alrevuelta/tubescreamer/img/img1.png

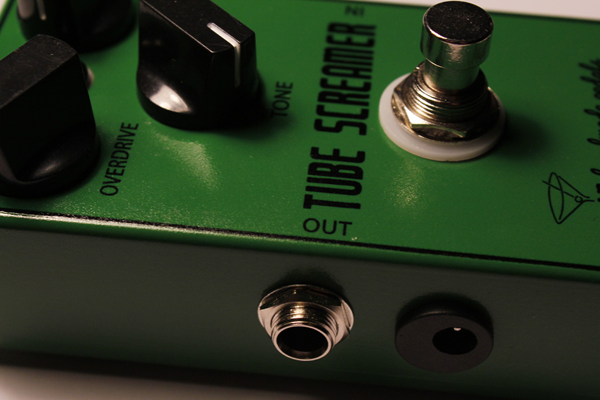
img/img1.png
