alrevuelta/tubescreamer/img/img2.png

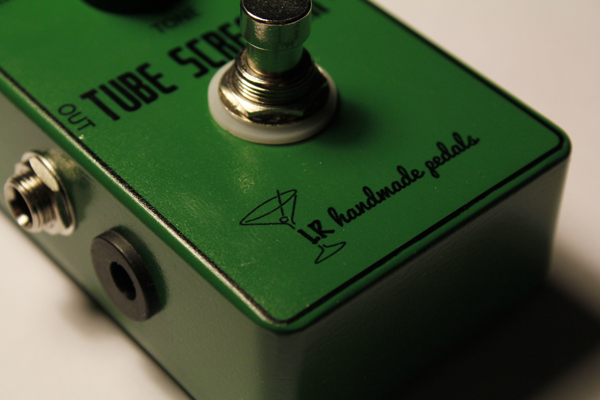
img/img2.png
