alrevuelta/tubescreamer/img/img3.png

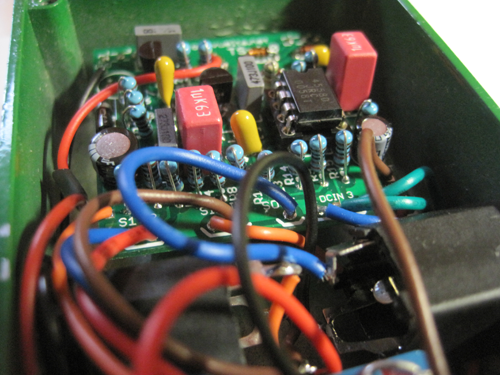
img/img3.png
