alrevuelta/tubescreamer/img/img6.png

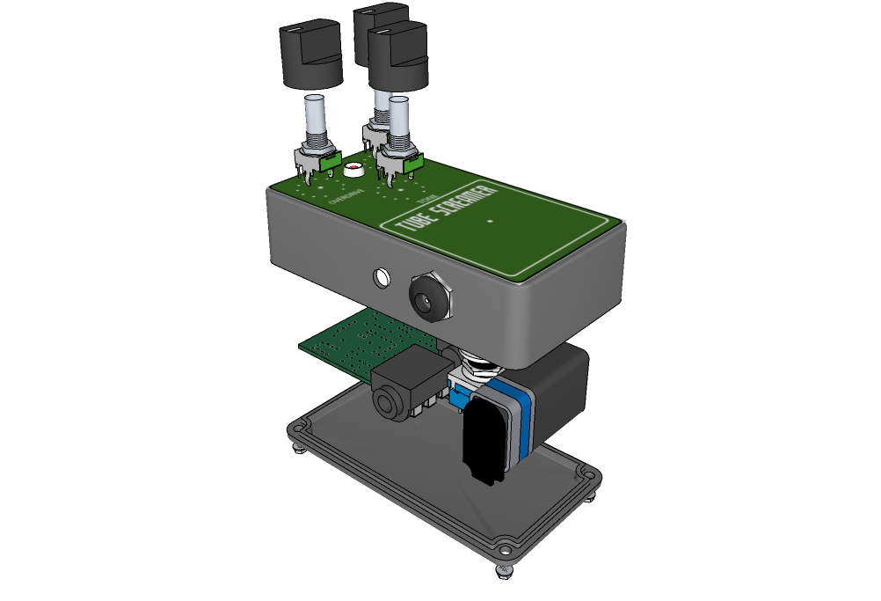
img/img6.png
