alrevuelta/tubescreamer/img/img7.png

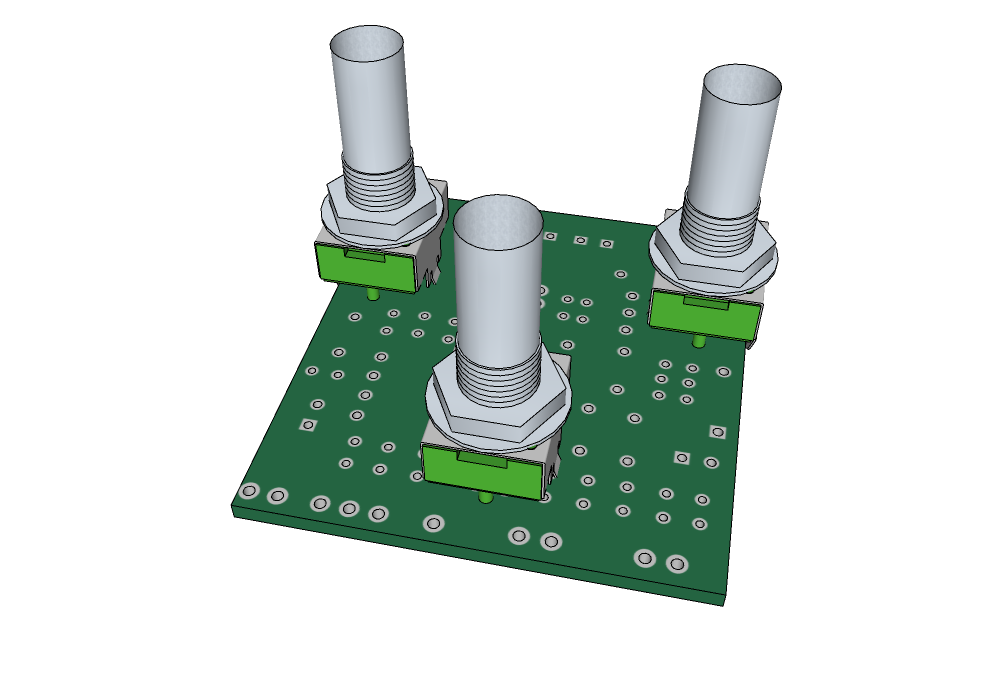
img/img7.png
