alrevuelta/tubescreamer/img/img8.png

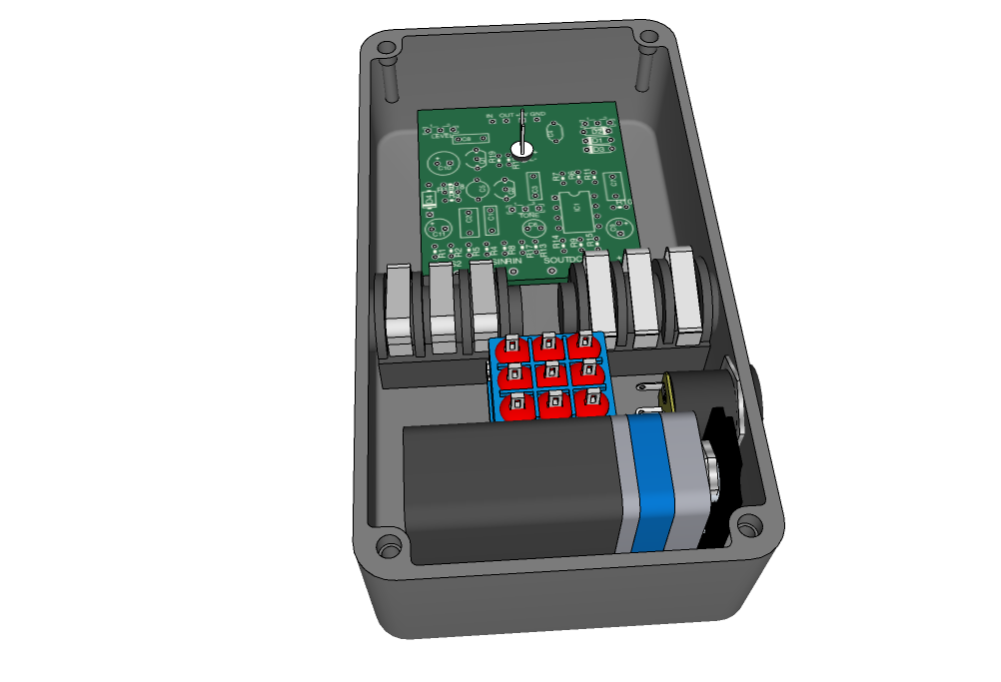
img/img8.png
