alrevuelta/tubescreamer/img/img9.png

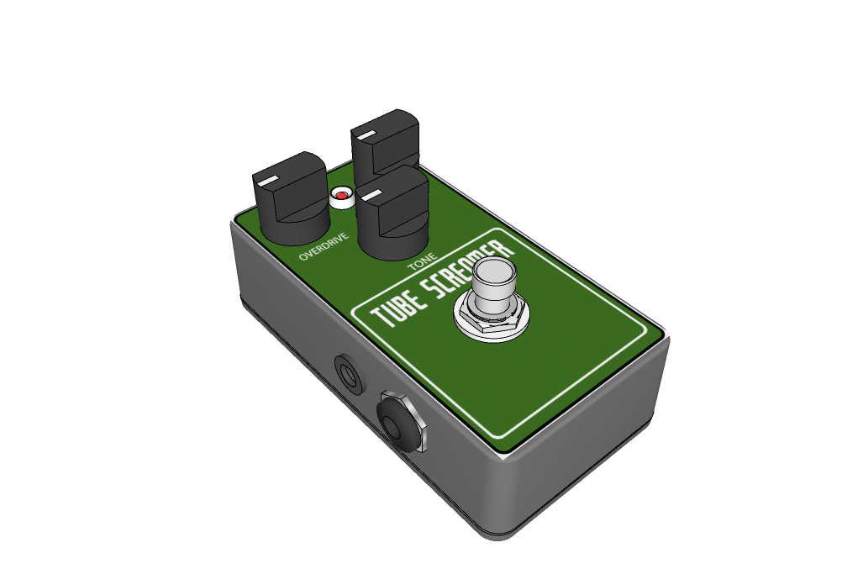
img/img9.png
