alrevuelta/tubescreamer/img/img10.png

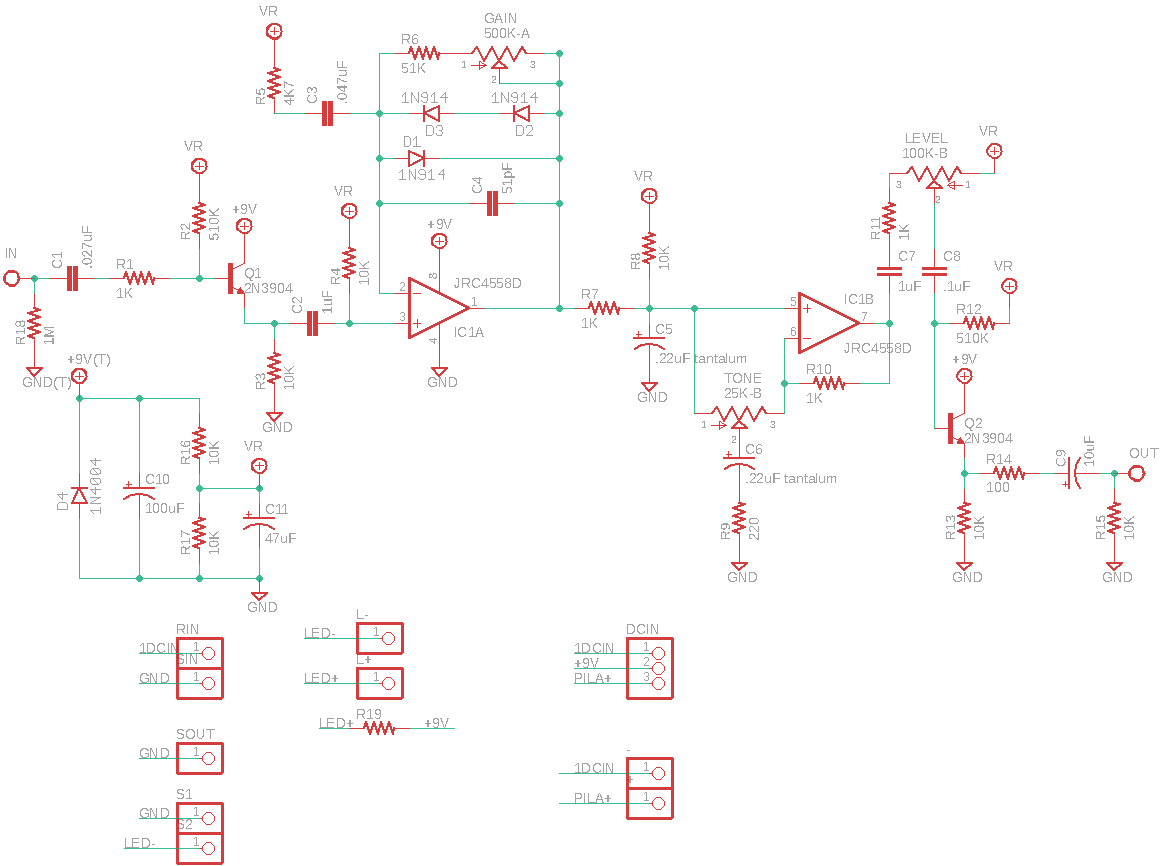
img/img10.png
