alrevuelta/tubescreamer/img/img11.png

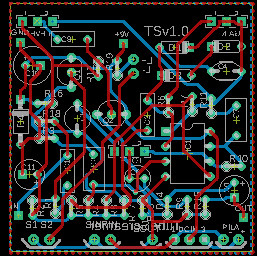
img/img11.png
